wang-junjian/meeting-terminal/export/parts/S03_TopCover.stl

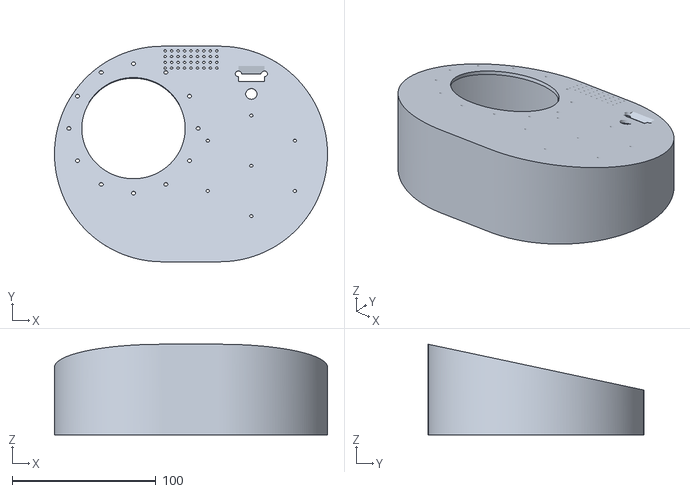
[picture p20: CAD file, 2026-07-23]
export/parts/S03_TopCover.stl
190.0 x 150.0 x 63.0
